torwanbukaj/ikea-brio-others-compatible-train-tracks-generator/pre-generated_parts_stl/brio/train_tracks_brio_intersect_90deg_100mmNP_40mmPP_b.stl

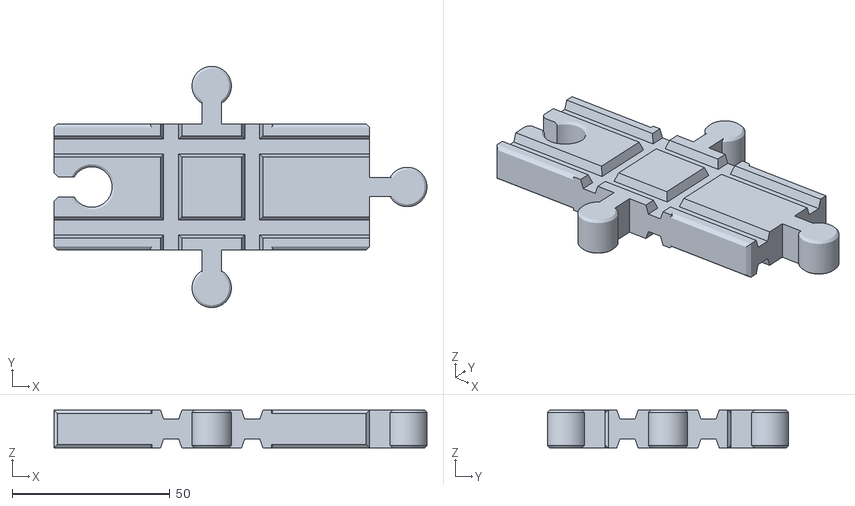
[picture p35: CAD file, 2023-01-09]
pre-generated_parts_stl/brio/train_tracks_brio_intersect_90deg_100mmNP_40mmPP_b.stl
118.2 x 76.5 x 12.0
