torwanbukaj/ikea-brio-others-compatible-train-tracks-generator/pre-generated_parts_stl/ikea/train_tracks_ikea_tester.stl

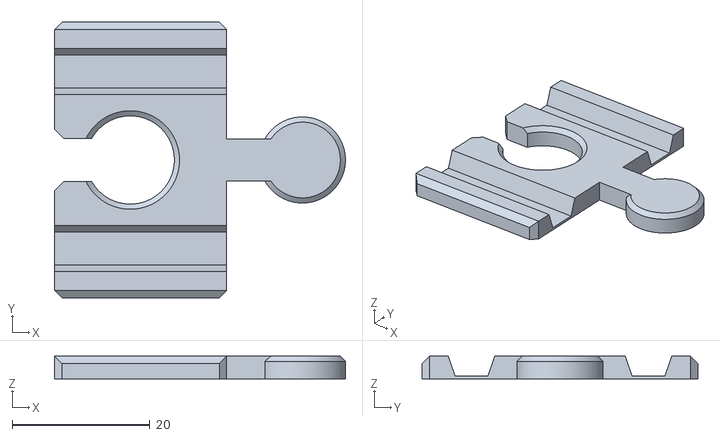
[picture p36: CAD file, 2023-01-09]
pre-generated_parts_stl/ikea/train_tracks_ikea_tester.stl
42.2 x 40.0 x 3.30
