torwanbukaj/ikea-brio-others-compatible-train-tracks-generator/pre-generated_parts_stl/brio/train_tracks_brio_straight50mm_NP.stl

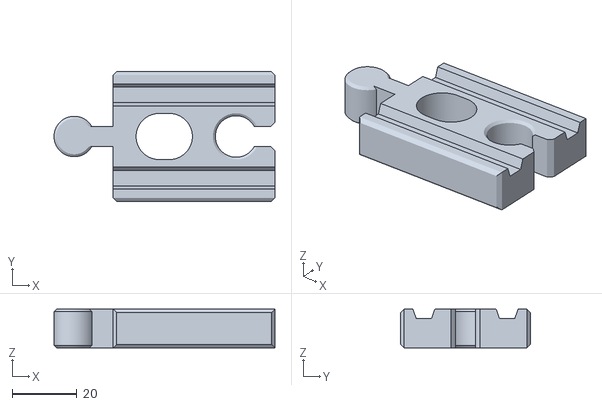
[picture p37: CAD file, 2023-01-09]
pre-generated_parts_stl/brio/train_tracks_brio_straight50mm_NP.stl
68.2 x 40.0 x 12.0
