torwanbukaj/ikea-brio-others-compatible-train-tracks-generator/pre-generated_parts_stl/ikea/train_tracks_ikea_lillabo_straight100mm_NP.stl

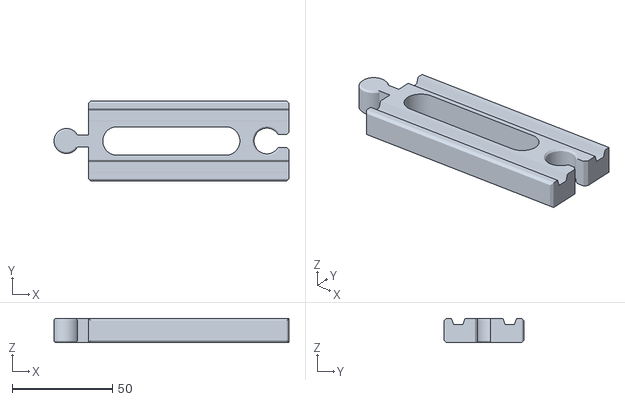
[picture p38: CAD file, 2023-01-09]
pre-generated_parts_stl/ikea/train_tracks_ikea_lillabo_straight100mm_NP.stl
117.2 x 40.0 x 12.0
