torwanbukaj/ikea-brio-others-compatible-train-tracks-generator/pre-generated_parts_stl/brio/train_tracks_brio_straight25mm_PP.stl

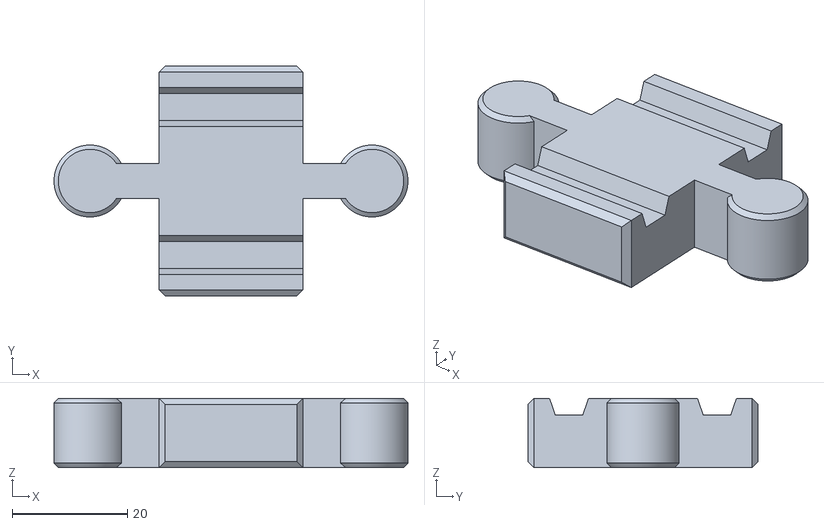
[picture p39: CAD file, 2023-01-09]
pre-generated_parts_stl/brio/train_tracks_brio_straight25mm_PP.stl
61.5 x 40.0 x 12.0
