torwanbukaj/ikea-brio-others-compatible-train-tracks-generator/pre-generated_parts_stl/ikea/train_tracks_ikea_lillabo_dogbone65.stl

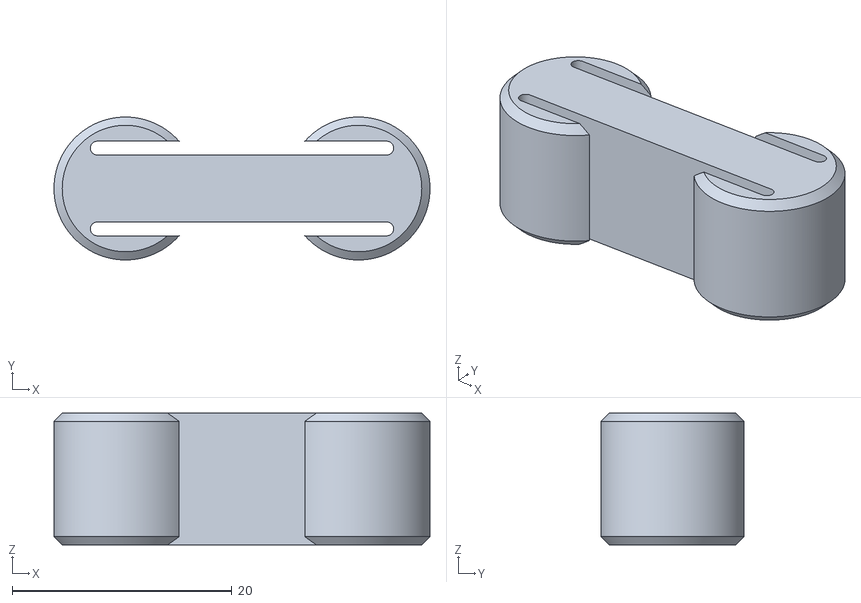
[picture p40: CAD file, 2023-01-09]
pre-generated_parts_stl/ikea/train_tracks_ikea_lillabo_dogbone65.stl
34.2 x 13.0 x 12.0
