torwanbukaj/ikea-brio-others-compatible-train-tracks-generator/pre-generated_parts_stl/brio/train_tracks_brio_bridge_pillar_14deg_r100mm_s205mm_p50mm.stl

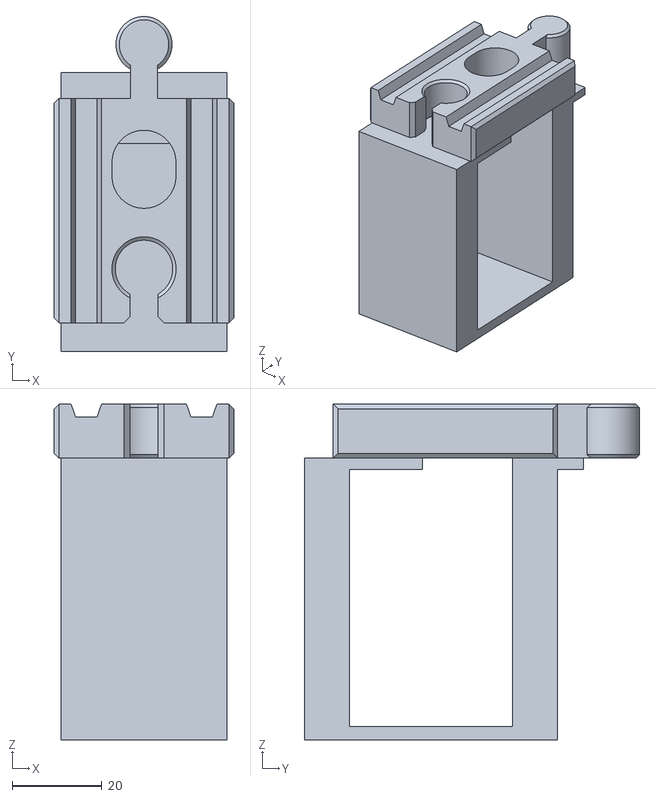
[picture p41: CAD file, 2023-01-09]
pre-generated_parts_stl/brio/train_tracks_brio_bridge_pillar_14deg_r100mm_s205mm_p50mm.stl
40.0 x 74.6 x 74.8
