torwanbukaj/ikea-brio-others-compatible-train-tracks-generator/pre-generated_parts_stl/ikea/train_tracks_ikea_lillabo_straight25mm_NP.stl

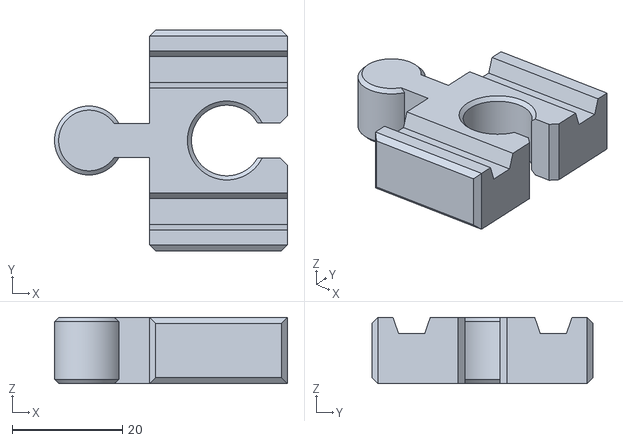
[picture p42: CAD file, 2023-01-09]
pre-generated_parts_stl/ikea/train_tracks_ikea_lillabo_straight25mm_NP.stl
42.2 x 40.0 x 12.0
