torwanbukaj/ikea-brio-others-compatible-train-tracks-generator/pre-generated_parts_stl/brio/train_tracks_brio_dogbone65.stl

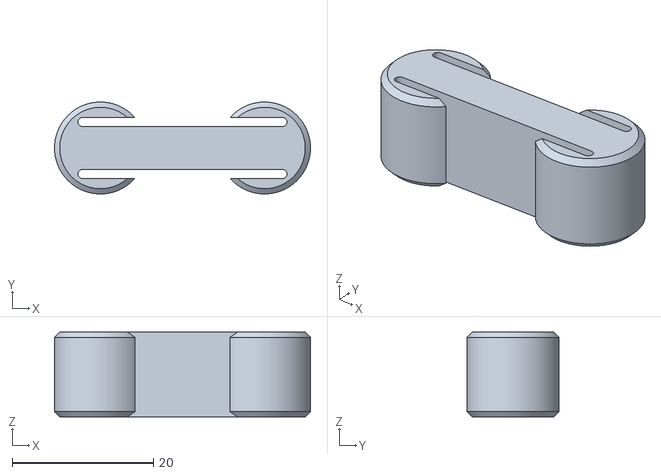
[picture p43: CAD file, 2023-01-09]
pre-generated_parts_stl/brio/train_tracks_brio_dogbone65.stl
36.2 x 13.0 x 12.0
