torwanbukaj/ikea-brio-others-compatible-train-tracks-generator/pre-generated_parts_stl/brio/train_tracks_brio_bridge_ground_14deg_r100mm_s205mm_p50mm.stl

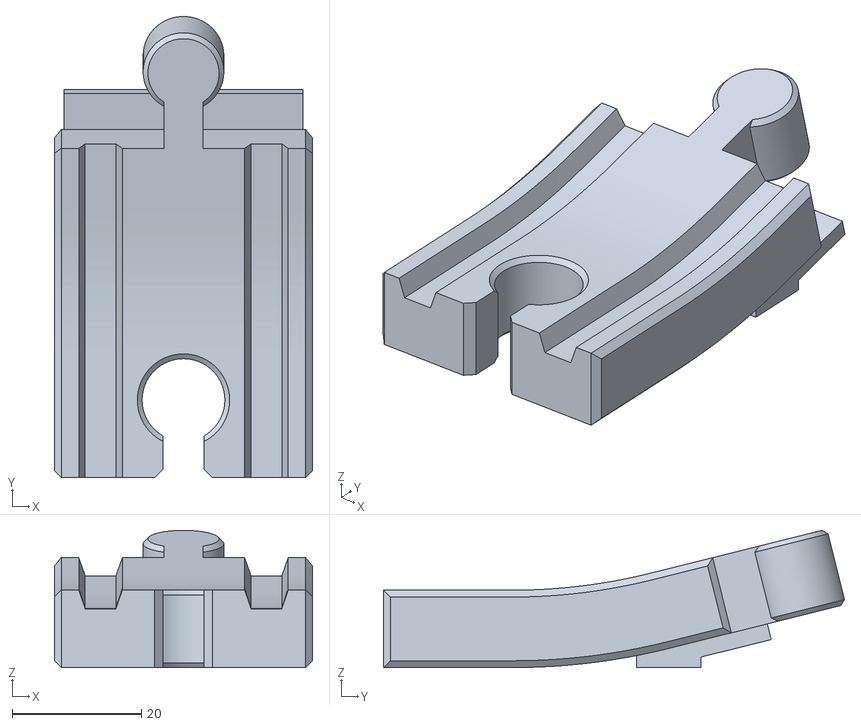
[picture p46: CAD file, 2023-01-09]
pre-generated_parts_stl/brio/train_tracks_brio_bridge_ground_14deg_r100mm_s205mm_p50mm.stl
40.0 x 71.4 x 21.3
