torwanbukaj/ikea-brio-others-compatible-train-tracks-generator/pre-generated_parts_stl/ikea/train_tracks_ikea_lillabo_bridge_ground_14deg_r100mm_s205mm_p50mm.stl

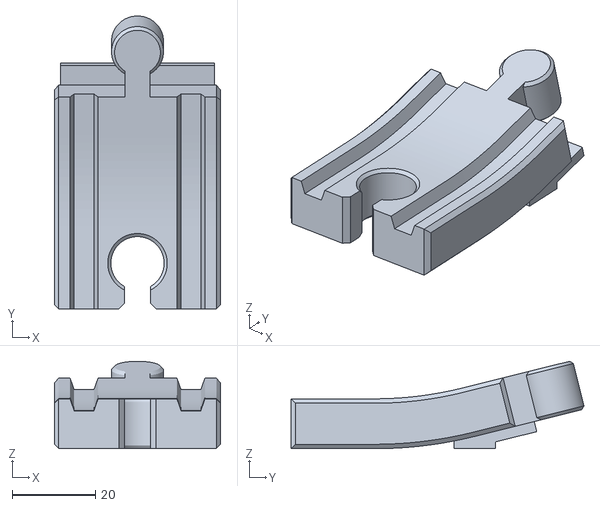
[picture p47: CAD file, 2023-01-09]
pre-generated_parts_stl/ikea/train_tracks_ikea_lillabo_bridge_ground_14deg_r100mm_s205mm_p50mm.stl
40.0 x 70.5 x 21.0
