torwanbukaj/ikea-brio-others-compatible-train-tracks-generator/pre-generated_parts_stl/brio/train_tracks_brio_straight25mm_NP.stl

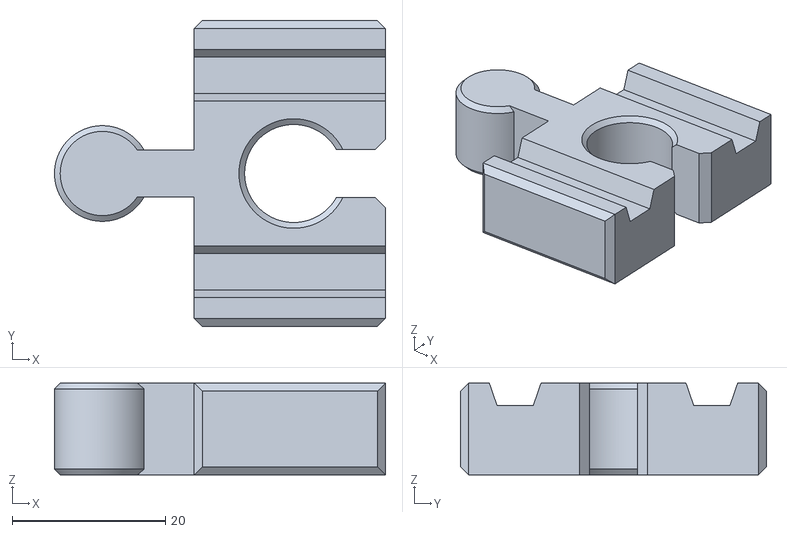
[picture p48: CAD file, 2023-01-09]
pre-generated_parts_stl/brio/train_tracks_brio_straight25mm_NP.stl
43.2 x 40.0 x 12.0
