torwanbukaj/ikea-brio-others-compatible-train-tracks-generator/pre-generated_parts_stl/ikea/train_tracks_ikea_lillabo_intersect_90deg_75mmNP_75mmNP_b.stl

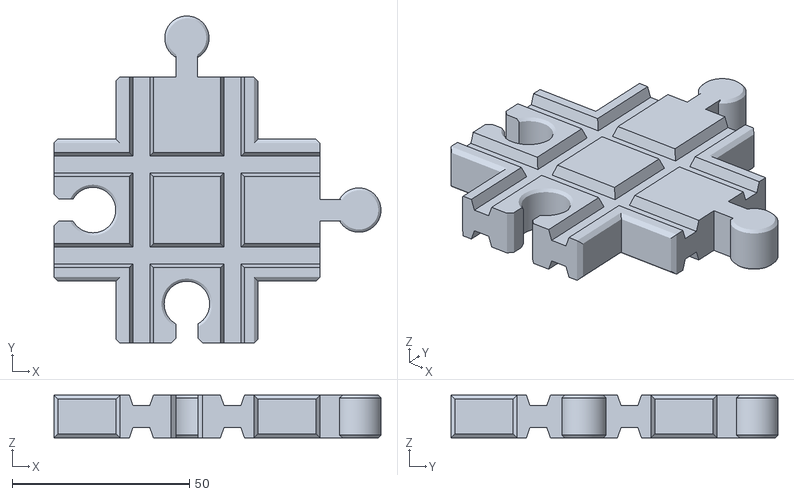
[picture p49: CAD file, 2023-01-09]
pre-generated_parts_stl/ikea/train_tracks_ikea_lillabo_intersect_90deg_75mmNP_75mmNP_b.stl
92.2 x 92.2 x 12.0
